Jb65uk/wakeback/hardware/carrier/out/step-bottom.png

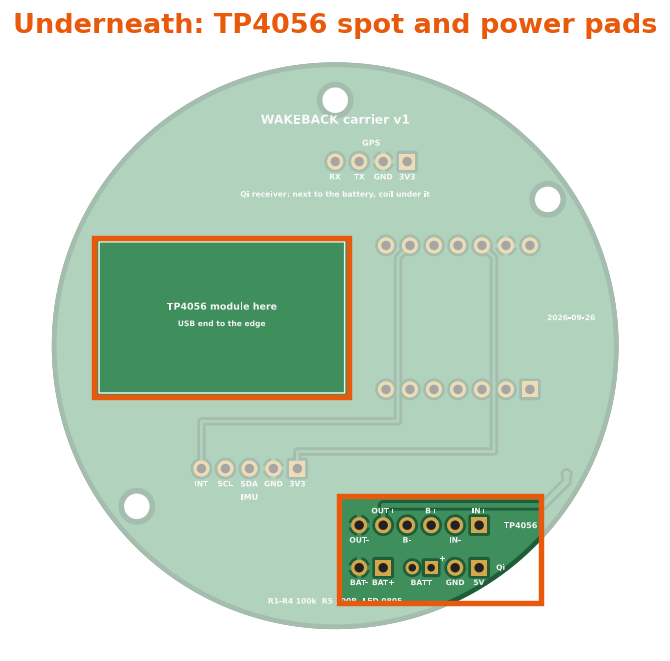
hardware/carrier/out/step-bottom.png
