Jb65uk/wakeback/hardware/carrier/out/step-gps.png

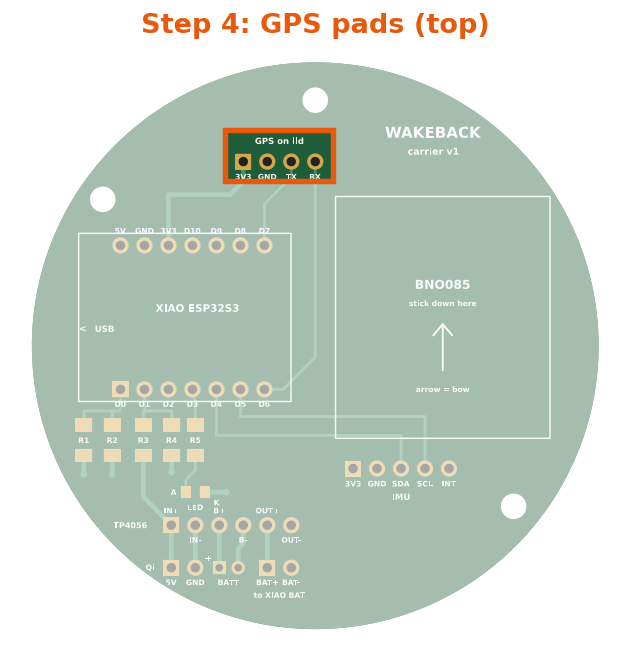
hardware/carrier/out/step-gps.png
