Jb65uk/wakeback/hardware/carrier/out/step-imu.png

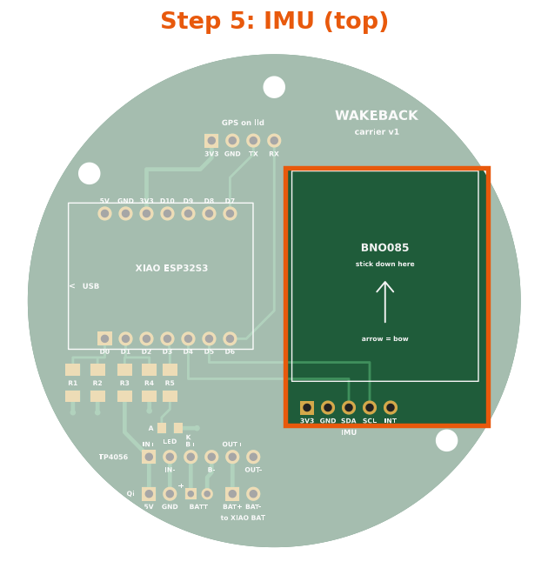
hardware/carrier/out/step-imu.png
