Jb65uk/wakeback/hardware/carrier/out/step-power.png

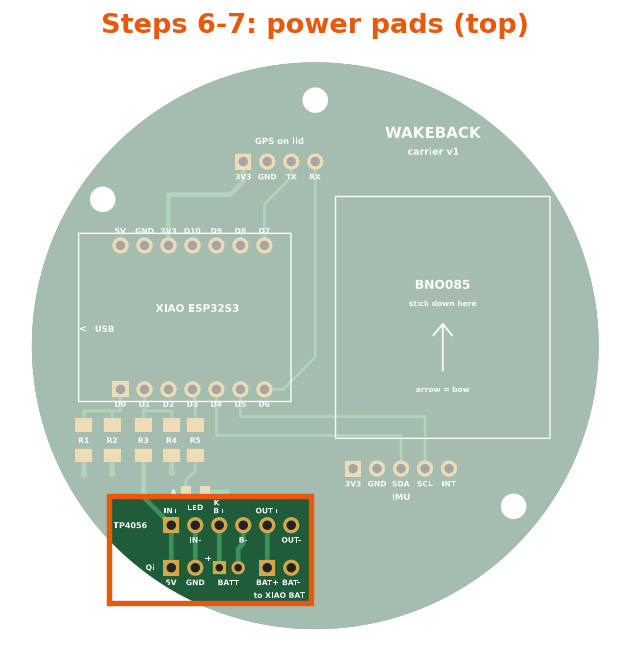
hardware/carrier/out/step-power.png
